elliotf/corexy-printer/main.scad

include <config.scad>;
include <positions.scad>;
include <boxcutter.scad>;
use <util.scad>;
use <belt_retainer.scad>;

module debug_lines() {
  color("red") % translate([20,0,0]) {
    cube([40,.5,.5],center=true);
  }
  color("green") % translate([0,20,0]) {
    cube([.5,40,.5],center=true);
  }
  color("blue") % translate([0,0,20]) {
    cube([.5,.5,40],center=true);
  }
}

module z_line_bearing() {
  difference() {
    hole(z_line_bearing_diam,z_line_bearing_thickness,resolution);
    hole(z_line_bearing_inner,z_line_bearing_thickness+1,resolution);
  }
}

module line_hole() {
  accurate_circle(3,resolution);
}

module zip_tie_hole(diam,width=zip_tie_width,thickness=zip_tie_thickness) {
  difference() {
    hole(diam+thickness*2,width,resolution);
    hole(diam,width+.1,resolution);
  }
}

module bevel_hole(diam,height,sides) {
  hull() {
    hole(diam+height*2,extrusion_height,sides);
    hole(diam,extrusion_height+height*2.2,sides);
  }
}

module line_bearing() {
  res = 64;

  module body() {
    for(side=[top,bottom]) {
      hull() {
        translate([0,0,-side*(line_bearing_thickness/4)]) {
          hole(line_bearing_effective_diam,line_bearing_thickness/2,res);
        }
        translate([0,0,-side*(line_bearing_thickness/2-0.05)]) {
          hole(line_bearing_diam,0.1,res);
        }
      }
    }
  }

  module holes() {
    hole(line_bearing_inner, line_bearing_thickness+1,res);
  }

  difference() {
    body();
    holes();
  }
}

module bevel_lipped_hole(diam=m3_diam,height=spacer,sides=8,lip_width=1) {
  difference() {
    hull() {
      translate([0,0,height/2]) {
        hole(diam+lip_width*2,height,sides);
      }

      translate([0,0,-.5]) {
        hole(diam+lip_width*2+height*2,1,sides);
      }
    }

    hole(diam,height*3,sides);
  }
}

module line_bearing_bevel(sides=[top,bottom], resolution=8, hole_resolution=8, spacing=line_bearing_thickness+line_bearing_washer_thickness*2) {
  difference() {
    for(side=sides) {
      translate([0,0,(spacing/2)*side]) {
        hull() {
          hole(line_bearing_inner+1,line_bearing_washer_thickness*2,resolution);
          translate([0,0,line_bearing_washer_thickness*side]) {
            hole(line_bearing_inner+4,line_bearing_washer_thickness,resolution);
          }
        }
      }
    }

    hole(line_bearing_inner,line_bearing_thickness*3,hole_resolution);
  }
}

module hotend() {
  e3d_hotend();
}

module e3d_hotend() {
  module body() {
    hotend_mount_height    = hotend_height_above_groove + hotend_groove_height + hotend_height_below_groove;

    translate([0,0,-hotend_height_above_groove/2]) {
      hole(hotend_mount_diam,hotend_height_above_groove,resolution);
    }
    translate([0,0,-hotend_height_above_groove-hotend_groove_height/2]) {
      hole(hotend_groove_diam,hotend_groove_height+1,resolution);
    }
    translate([0,0,-hotend_height_above_groove-hotend_groove_height-hotend_height_below_groove/2-10]) {
      hole(hotend_mount_diam,hotend_height_below_groove+20,resolution);
    }

    num_fins      = 11;
    fin_thickness = 1;
    fin_spacing   = 2.5;

    translate([0,0,-hotend_dist_to_heatsink_bottom+fin_thickness/2]) {
      for(z=[0:10]) {
        translate([0,0,fin_spacing*z]) {
          hole(hotend_heatsink_diam,fin_thickness,resolution);
        }
      }
    }

    translate([0,0,-hotend_len]) {
      hull() {
        translate([0,0,0.5]) {
          hole(.5,1,36);
        }
        translate([0,0,3.5]) {
          hole(4,2,36);
        }
      }

      translate([0,-20/2+4.5,5+11.5/2]) {
        cube([16,20,11.5],center=true);
      }
    }
  }

  module holes() {
    //hole(filament_diam,hotend_len*3,8);
  }

  difference() {
    body();
    holes();
  }
}

module jhead_hotend() {
  module body() {
    height_groove_and_above = hotend_clamped_height;
    height_below_groove = hotend_len - height_groove_and_above;

    translate([0,0,-hotend_height_above_groove/2]) {
      hole(hotend_diam,hotend_height_above_groove,90);
    }
    translate([0,0,-hotend_height_above_groove-hotend_groove_height/2]) {
      hole(hotend_groove_diam,hotend_groove_height,90);
    }
    translate([0,0,-height_groove_and_above-height_below_groove/2]) {
      hole(hotend_diam,height_below_groove,90);
    }
  }

  module holes() {
    hole(filament_diam,hotend_len*3,8);
  }

  difference() {
    body();
    holes();
  }
}

module motor() {
  difference() {
    translate([0,0,-motor_side/2]) cube([motor_side,motor_side,motor_side],center=true);
    for(end=[left,right]) {
      for(side=[front,rear]) {
        translate([motor_hole_spacing/2*side,motor_hole_spacing/2*end,0]) cylinder(r=motor_screw_diam/2,h=100,center=true);
      }
    }
  }

  translate([0,0,motor_shaft_len/2]) cylinder(r=motor_shaft_diam/2,h=motor_shaft_len,center=true);
}

module motor_sheet_holes() {
  accurate_circle(z_motor_shoulder_diam,resolution);

  for(x=[left,right]) {
    for(y=[top,bottom]) {
      translate([nema17_hole_spacing/2*x,nema17_hole_spacing/2*y]) {
        accurate_circle(nema17_screw_diam,resolution);
      }

      rotate([0,0,45]) {
        translate([nema14_hole_spacing/2*x,nema14_hole_spacing/2*y]) {
          accurate_circle(nema14_screw_diam,resolution);
        }
      }
    }
  }
}

module hotend_zip_tie_holes() {
  hotend_clearance = 0.1;
  hotend_res = resolution;
  above_height = hotend_height_above_groove+hotend_clearance*2;
  translate([0,-hotend_diam/2,0]) {
    cube([hotend_groove_diam-0.2,hotend_diam,30],center=true);
  }

  for(side=[top,bottom]) {
    translate([0,-hotend_mount_diam/2,side*(hotend_groove_height)]) {
      cube([hotend_mount_diam-0.2,hotend_mount_diam,hotend_groove_height],center=true);
    }
  }

  // zip tie restraint
  zip_tie_hole(hotend_diam + wall_thickness);

  rotate([0,0,-45]) {
    translate([hotend_diam/2-3,-hotend_diam/2,0]) {
      cube([hotend_diam,hotend_diam,hotend_groove_height+hotend_height_above_groove*2+0.05],center=true);
    }
  }
}

module hotend_groove_mount_void() {
  hotend_clearance = 0.1;
  hotend_res = resolution;
  above_height = hotend_height_above_groove+hotend_clearance*2;
  rotate([0,0,90]) {
    translate([0,0,-hotend_height_above_groove-hotend_groove_height/2]) {
      translate([0,-hotend_diam/2,0]) {
        cube([hotend_groove_diam,hotend_diam,30],center=true);
      }
    }

    translate([0,0,-above_height/2+hotend_clearance]) {
      hole(hotend_groove_diam+hotend_clearance,above_height,hotend_res);
      translate([0,-hotend_diam/2,0]) {
        cube([hotend_diam,hotend_diam,above_height],center=true);
      }
    }

    // zip tie restraint
    translate([0,0,-above_height/2]) {
      zip_tie_hole(hotend_diam + wall_thickness*2.5);
    }

    translate([0,0,-hotend_clamped_height-10+hotend_clearance]) {
      hole(hotend_diam+hotend_clearance,20,hotend_res);
      translate([0,-hotend_diam/2,0]) {
        cube([hotend_diam,hotend_diam,20],center=true);
      }
    }
  }
}

module x_carriage() {
  body_side        = rear;
  fan_side         = 30;
  fan_diam         = fan_side-wall_thickness*2;
  fan_screw_diam   = 2.6;
  fan_screw_depth  = 7;
  fan_thickness    = 10;
  fan_pos_y        = front*(x_bearing_diam/2+30/2+wall_thickness/2);
  fan_pos_z        = hotend_z-hotend_dist_to_heatsink_bottom+fan_side/2;
  fan_hole_spacing = 24;
  heatsink_pos_z   = hotend_z-hotend_len+hotend_nozzle_to_bottom_fin+hotend_heatsink_height/2;
  heatsink_pos_z   = hotend_z-hotend_dist_to_heatsink_bottom+hotend_heatsink_height/2;

  bearing_body_wall_thickness = top_line_pos_y-x_bearing_diam/2;
  bearing_body_diam = x_bearing_diam+wall_thickness*3;
  bearing_body_diam = x_bearing_diam + bearing_body_wall_thickness*2;

  body_depth  = top_line_pos_y - bottom_line_pos_y;
  body_height = x_rod_spacing;

  tuner_mount_width  = x_carriage_width;
  tuner_mount_depth  = tuner_shaft_screwed_diam+wall_thickness*3;
  tuner_mount_height = tuner_shaft_screwed_len;

  bottom_top_dist_z     = top_line_pos_z - bottom_line_pos_z;
  bottom_top_dist_y     = top_line_pos_y - bottom_line_pos_y;
  bottom_top_dist_angle = sqrt(pow(bottom_top_dist_z,2)+pow(bottom_top_dist_y,2));
  bottom_top_line_angle = atan2(bottom_top_dist_z,bottom_top_dist_y);

  line_hole_opening     = 1.1;

  tuner_rotate_z = 10;
  module position_tuner() {
    translate([tuner_pos_x,tuner_pos_y,top_line_pos_z]) {
      rotate([0,0,tuner_rotate_z]) {
        rotate([0,90,0]) {
          children();
        }
      }
    }
  }

  module body() {
    // bearing holders
    hull() {
      for(side=[top,bottom]) {
        translate([0,0,x_rod_spacing/2*side]) {
          rotate([0,90,0]) {
            hole(bearing_body_diam,x_carriage_width,resolution);
          }
        }
      }
    }

    // tuner retainer body
    hull() {
      translate([0,tuner_pos_y,tuner_shoulder_pos_z-tuner_mount_height/2]) {
        for(y=[front]) {
          for(z=[top,bottom]) {
            translate([0,y*(tuner_mount_depth/2-rounded_diam/2),z*(tuner_mount_height/2-rounded_diam/2)]) {
              rotate([0,90,0]) {
                hole(rounded_diam,tuner_mount_width,resolution);
              }
            }
          }
        }
        for(y=[rear]) {
          for(z=[top,bottom]) {
            translate([0,y*(tuner_mount_depth/2-rounded_diam/2+wall_thickness*z),z*(tuner_mount_height/2-rounded_diam/2)]) {
              rotate([0,90,0]) {
                hole(rounded_diam,tuner_mount_width,resolution);
              }
            }
          }
        }
      }
      // tuner mounting
      for(side=[left,right]) {
        mirror([1-side,0,0]) {
          position_tuner() {
            translate([tuner_anchor_screw_hole_pos_x,tuner_anchor_screw_hole_pos_y,tuner_anchor_screw_hole_pos_z]) {
              rotate([0,90,0]) {
                translate([0,0,2.5]) {
                  hole(tuner_anchor_screw_hole_diam+wall_thickness*2,3,resolution);
                }
              }
            }
          }
        }
      }
    }

    // hotend mount
    hull() {
      translate([-x_carriage_width/2+1,0,x_rod_spacing/2]) {
        rotate([0,90,0]) {
          hole(bearing_body_diam,2,8);
        }
      }
      translate([0,hotend_y,hotend_z-hotend_height_above_groove/2]) {
        hole(hotend_mount_diam+wall_thickness*3,0.1,resolution);

        translate([-x_carriage_width/2+hotend_groove_diam/2,0,0]) {
          hole(hotend_groove_diam,0.1,8);
        }
      }
      translate([0,hotend_y,fan_pos_z]) {
        hole(hotend_diam+wall_thickness*3,fan_side,resolution);
      }
      translate([-x_carriage_width/2+wall_thickness*2,0,fan_pos_z]) {
        cube([wall_thickness*4,1,fan_side],center=true);
      }
      translate([x_carriage_width/2-1,-bearing_body_diam/4,fan_pos_z]) {
        cube([2,bearing_body_diam/2,fan_side],center=true);
      }
      translate([-x_carriage_width/2+wall_thickness*2,fan_pos_y,fan_pos_z]) {
        for(y=[front]) {
          for(z=[top,bottom]) {
            translate([0,(fan_side/2-rounded_diam/2)*y,(fan_side/2-rounded_diam/2)*z]) {
              rotate([0,90,0]) {
                hole(rounded_diam,wall_thickness*4,resolution);
              }
            }
          }
        }
      }
    }

    rounded_diam = 5;
    // conntect top bearing to tuner mount
    hull() {
      translate([0,tuner_pos_y,tuner_shoulder_pos_z-tuner_mount_height/2]) {
        translate([0,front*(tuner_mount_depth/2-rounded_diam/2),tuner_mount_height/2-rounded_diam/2]) {
          rotate([0,90,0]) {
            hole(rounded_diam,tuner_mount_width,resolution);
          }
        }
      }

      translate([0,0,x_rod_spacing/2]) {
        rotate([0,90,0]) {
          hole(bearing_body_diam,x_carriage_width,resolution);
        }
      }
    }
  }

  module holes() {
    // hotend mount
    hotend_groove_depth = (hotend_diam - hotend_groove_diam)/2;
    translate([0,hotend_y,hotend_z-hotend_height_above_groove-hotend_groove_height/2]) {
      zip_tie_hole(hotend_groove_diam+wall_thickness*3);
    }

    translate([0,hotend_y,hotend_z-hotend_len/2]) {
      hull() {
        for(r=[0,-60]) {
          rotate([0,0,r]) {
            translate([20,1,0]) {
              cube([40,2,hotend_len+10],center=true);
            }
          }
        }
      }
    }
    translate([hotend_groove_diam*.8,hotend_y-hotend_groove_diam,hotend_z-hotend_len/2]) {
      //cube([hotend_groove_diam,hotend_groove_diam*1.5,hotend_len+1],center=true);
    }

    groove_slop = 0.1;
    translate([0,hotend_y,hotend_z-groove_slop/2]) {
      hole(hotend_mount_diam,hotend_height_above_groove*2,resolution);

      translate([20,0,0]) {
        cube([40,hotend_mount_diam-0.1,hotend_height_above_groove*2],center=true);
      }
    }
    translate([0,hotend_y,hotend_z-hotend_height_above_groove-hotend_groove_height/2]) {
      hole(hotend_groove_diam,hotend_groove_height*2,resolution);

      translate([20,0,0]) {
        cube([40,hotend_groove_diam-0.1,hotend_groove_height*2],center=true);
      }
    }
    translate([0,hotend_y,hotend_z-hotend_height_above_groove-hotend_groove_height-10+groove_slop/2]) {
      hole(hotend_mount_diam,20,resolution);

      translate([20,0,0]) {
        cube([40,hotend_mount_diam-0.1,20],center=true);
      }
    }
    hull() {
      translate([-x_carriage_width/2,fan_pos_y,fan_pos_z]) {
        rotate([0,90,0]) {
          hole(fan_diam,fan_thickness*3,resolution);
        }
      }
      translate([0,hotend_y,fan_pos_z]) {
        hole(hotend_diam,1,resolution);
      }
    }
    translate([-x_carriage_width/2,fan_pos_y,fan_pos_z]) {
      for(y=[front,rear]) {
        for(z=[top,bottom]) {
          translate([0,fan_hole_spacing/2*y,fan_hole_spacing/2*z]) {
            rotate([0,90,0]) {
              hole(fan_screw_diam,fan_screw_depth*2,8);
            }
          }
        }
      }
    }
    translate([0,hotend_y,heatsink_pos_z-0.05]) {
      hole(hotend_diam,hotend_heatsink_height+0.1,resolution);

      translate([20,0,0]) {
        cube([40,hotend_diam-0.1,hotend_heatsink_height+0.1],center=true);
      }
    }

    tuner_hollow_nut_height = tuner_mount_height*.75;
    // tuner mounting
    for(side=[left,right]) {
      mirror([1-side,0,0]) {
        position_tuner() {
          translate([tuner_anchor_screw_hole_pos_x,tuner_anchor_screw_hole_pos_y,tuner_anchor_screw_hole_pos_z]) rotate([0,90,0]) {
            rotate([0,0,tuner_rotate_z]) {
              hole(tuner_anchor_screw_hole_diam,12,8);
            }
          }
        }
      }
      translate([tuner_pos_x*side,tuner_pos_y,0]) {
        // main hole and screw hole
        translate([0,0,tuner_shoulder_pos_z]) {
          hole(tuner_shaft_screw_diam,tuner_mount_height*2+1,8);
          hole(tuner_shaft_screwed_diam,21,8);

          translate([0,0,-tuner_mount_height-tuner_hollow_nut_height/2]) {
            hole(tuner_nut_max_diam,tuner_hollow_nut_height,resolution);
          }
        }
      }
    }

    // reinforcements
    for(z=[1,3,5]) {
      translate([0,tuner_pos_y+tuner_mount_depth/2+1,tuner_shoulder_pos_z-3*z]) {
        cube([1,tuner_mount_depth+tuner_shaft_screwed_diam,1],center=true);
      }
    }

    // line path
    translate([0,top_line_pos_y,top_line_pos_z]) {
      rotate([bottom_top_line_angle,0,0]) {
        rotate([0,90,0]) {
          hole(line_hole_opening,x_carriage_width+1,8);
        }
      }
    }
    hull() {
      translate([0,-x_bearing_diam/8,0]) {
        rotate([0,90,0]) {
          hole(line_hole_opening*2,x_carriage_width+1,8);
        }
      }
      translate([0,bottom_line_pos_y,bottom_line_pos_z]) {
        rotate([bottom_top_line_angle,0,0]) {
          rotate([0,90,0]) {
            hole(line_hole_opening,x_carriage_width+1,8);
          }
        }
      }
    }
    front_to_back_line_path_diam = bottom_top_dist_angle-line_hole_opening;
    for(side=[left,right]) {
      translate([(x_carriage_width/2-front_to_back_line_path_diam/2-.5)*side,top_line_pos_y-bottom_top_dist_y/2,top_line_pos_z-bottom_top_dist_z/2]) {
        rotate([bottom_top_line_angle,0,0]) {
          difference() {
            translate([side*(bottom_top_dist_angle/2-2),2,0]) {
              cube([bottom_top_dist_angle/2+2,bottom_top_dist_angle+4,line_hole_opening],center=true);
            }
            hole(front_to_back_line_path_diam,line_hole_opening+1,resolution);
          }
        }
      }
    }
    translate([extrusion_height,-1,x_rod_spacing/2+x_bearing_diam/2]) {
      rotate([0,0,0]) {
        cube([x_carriage_width,5,x_bearing_diam],center=true);
      }
    }
    translate([extrusion_height,0,-x_rod_spacing/2-x_bearing_diam]) {
      rotate([45,0,0]) {
        cube([x_carriage_width,x_bearing_diam*1.5,x_bearing_diam*1.5],center=true);
      }
    }

    for(side=[top,bottom]) {
      translate([0,0,x_rod_spacing/2*side]) {
        rotate([0,90,0]) {
          // bearing hole
          hole(x_bearing_diam,x_carriage_width+1,16);
          // beveled opening
          for(end=[left,right]) {
            hull() {
              translate([0,0,(x_carriage_width/2)*end]) {
                hole(x_bearing_diam,3,16);
                translate([0,0,.5*end]) {
                  hole(x_bearing_diam+1,1,16);
                }
              }
            }
          }
        }
      }
    }

    translate([extrusion_height,-x_bearing_diam/4,0]) {
      //cube([x_carriage_width,x_bearing_diam/2,x_rod_spacing],center=true);
    }

    translate([0,hotend_y,hotend_z]) {
      % hotend();
    }

    translate([-x_carriage_width/2-5,fan_pos_y,fan_pos_z]) {
      % cube([fan_thickness,fan_side,fan_side],center=true);
    }
  }
  translate([0,top_line_pos_y,top_line_pos_z]) {
    //color("green") % cube([x_carriage_width+60,0.8,0.8],center=true);
  }
  translate([0,bottom_line_pos_y,bottom_line_pos_z]) {
    //color("red") % cube([x_carriage_width+60,0.8,0.8],center=true);
  }

  for(side=[left,right]) {
    mirror([1+side,0,0]) {
      position_tuner() {
        % tuner();
      }
    }
  }

  difference() {
    body();
    holes();
  }

  % for(side=[top,bottom]) {
    translate([0,0,x_rod_spacing/2*side]) {
      rotate([0,90,0]) {
        cylinder(r=x_bearing_diam/2,h=x_bearing_len,center=true);
      }
    }
  }

  translate([0,hotend_y,hotend_z]) {
    //% hotend();
  }
}

module y_carriage() {
  line_bearing_x              = (y_rod_x - y_carriage_line_bearing_x);
  line_bearing_opening_height = line_bearing_thickness*2+line_bearing_washer_thickness*3;
  rod_hole_diam               = x_rod_diam + rod_slop;
  x_rod_clamp_len             = y_carriage_width;

  rounded_diam = y_rod_diam+rod_slop+min_material_thickness*4;
  total_height = x_rod_spacing + rounded_diam;

  module body() {
    // main body, hold x rods
    hull() {
      for(side=[top,bottom]) {
        translate([x_rod_clamp_len/2,-x_rod_diam,x_rod_spacing/2*side]) {
          rotate([0,90,0]) {
            hole(rounded_diam,x_rod_clamp_len,resolution);
          }
        }

        translate([x_rod_clamp_len/2,front*(y_bearing_len/2-line_bearing_diam*.75),0]) {
          rotate([0,90,0]) {
            hole(line_bearing_diam,x_rod_clamp_len,resolution);
          }
        }

        translate([x_rod_clamp_len/2,rear*(y_bearing_len/2-rounded_diam/4),(total_height/2-rounded_diam/4)*side]) {
          rotate([0,90,0]) {
            hole(rounded_diam/2,x_rod_clamp_len,resolution);
          }
        }

        intersection() {
          translate([y_bearing_diam/2,0,0]) {
            cube([y_bearing_diam,y_bearing_len*2,y_bearing_diam*2],center=true);
          }
          rotate([90,0,0]) {
            hole(y_bearing_diam+6,y_bearing_len,resolution);
          }
        }
      }
      translate([line_bearing_x,y_carriage_line_bearing_y,y_carriage_line_bearing_z]) {
        cube([line_bearing_diam,line_bearing_diam+spacer*2+extrusion_width*6,line_bearing_opening_height+2],center=true);
      }
    }
  }

  module holes() {
    // x rods and clamps
    for(side=[top,bottom]) {
      translate([x_rod_clamp_len/2,0,x_rod_spacing/2*side]) {
        rotate([0,90,0]) {
          hole(rod_hole_diam+rod_slop,x_rod_clamp_len+4,16);

          for(end=[left,right]) {
            translate([0,0,(x_rod_clamp_len/2+.5)*end]) {
              hull() {
                hole(rod_hole_diam,3,16);
                hole(rod_hole_diam+1,1,16);
              }
            }
          }
        }

        translate([-extrusion_height,20,0]) {
          cube([x_rod_clamp_len,40,2],center=true);
        }
        hull() {
          translate([-extrusion_height,0,0]) {
            rotate([0,90,0]) {
              hole(2,x_rod_clamp_len,16);
            }
            translate([0,-x_rod_diam,0]) {
              rotate([0,90,0]) {
                hole(2,x_rod_clamp_len,16);
              }
            }
          }
        }
      }
    }

    // zip tie to secure the carriage to the y rod bearing
    translate([0,-rod_hole_diam/2-zip_tie_width,0]) {
      rotate([90,0,0]) {
        zip_tie_hole(y_bearing_diam+min_material_thickness*2);
      }
    }

    // y rod bearing and clamp
    translate([0,0,0]) {
      rotate([90,0,0]) {
        hole(y_bearing_diam,y_bearing_len*2,16);
      }
    }

    // bearing/line-related holes
    translate([line_bearing_x-line_bearing_effective_diam/2-0.4,y_carriage_line_bearing_y,0]) {
      translate([0,-y_bearing_len,to_front_line_z]) {
        rotate([90,0,0]) {
          hole(2,y_bearing_len*2,8);
        }
      }
      translate([0,y_bearing_len,to_rear_line_z]) {
        rotate([90,0,0]) {
          hole(2,y_bearing_len*2,8);
        }
      }
    }
    translate([line_bearing_x,y_carriage_line_bearing_y,y_carriage_line_bearing_z]) {
      // bearing/clamp screw
      hole(line_bearing_inner+rod_slop,50,8);

      // captive nut
      translate([0,0,-total_height/2]) {
        hole(line_bearing_nut_diam,4,6);
      }

      hull() {
        hole(line_bearing_diam + spacer*2,line_bearing_opening_height,resolution);
        // room for belt/filament
        translate([line_bearing_diam/2,0,0]) {
          cube([line_bearing_diam+spacer*2,line_bearing_diam+spacer*2,line_bearing_opening_height],center=true);
        }
      }

      for (side=[top,bottom]) {
        translate([0,0,(line_bearing_thickness/2+line_bearing_washer_thickness/2)*side]) {
          % line_bearing();
        }
      }
    }
  }

  module bridges() {
    for(side=[top,bottom]) {
      translate([line_bearing_x,y_carriage_line_bearing_y,y_carriage_line_bearing_z+side*(line_bearing_washer_thickness/2+line_bearing_thickness/2)]) {
        line_bearing_bevel([side]);
      }
    }
  }

  difference() {
    body();
    holes();
  }
  bridges();

  translate([0,0,0]) {
    rotate([90,0,0]) {
      % cylinder(r=y_bearing_diam/2,h=y_bearing_len,center=true);
    }
  }
}

module handle() {
  module body() {
    hull() {
      translate([0,-handle_attachment_height/2,0]) {
        cube([handle_hole_width+handle_material_width*2,handle_attachment_height,sheet_thickness],center=true);
      }

      for(x=[left,right]) {
        translate([x*(handle_hole_width/2+handle_material_width/2-5),handle_hole_height+handle_material_width/2,0]) {
          hole(handle_material_width,sheet_thickness,resolution);
        }
      }
    }
  }

  module holes() {
    hull() {
      for(x=[left,right]) {
        translate([x*(handle_hole_width/2-handle_material_width/2),handle_hole_height/2+top*(handle_hole_height/2-handle_material_width/2),0]) {
          hole(handle_material_width,sheet_thickness+1,resolution);
        }
        translate([x*(handle_hole_width/2-handle_material_width/2),handle_hole_height/2+bottom*(handle_hole_height/2-handle_material_width/2),0]) {
          hole(handle_material_width,sheet_thickness+1,resolution);
        }
      }
    }
  }

  difference() {
    body();
    holes();
  }
}

module front_sheet() {
  rounded_diam = bc_shoulder_width*2;

  module body() {
    width  = front_sheet_width + sheet_thickness*2 + bc_shoulder_width*2;
    height = sheet_height      + sheet_thickness + bc_shoulder_width;
    intersection() {
      box_side([front_sheet_width,sheet_height],[0,4,4,4]);
      translate([0,-sheet_thickness/2-bc_shoulder_width/2]) {
        hull() {
          for(x=[left,right]) {
            for(y=[top,bottom]) {
              translate([x*(width/2-rounded_diam/2),y*(height/2-rounded_diam/2),0]) {
                accurate_circle(rounded_diam,resolution);
              }
            }
          }
        }
      }
    }
  }

  module holes() {
    translate([0,-sheet_pos_z,0]) {
      translate([0,top_sheet_pos_z,0]) {
        box_holes_for_side(front_sheet_width,4);
      }

      for(side=[left,right]) {
        translate([y_rod_x*side,0,0]) {
          accurate_circle(y_rod_diam-laser_cut_kerf*2,64);
        }

        translate([return_line_x*side,return_line_z,0]) {
          line_hole();
        }

        translate([xy_line_x*side,to_front_line_z,0]) {
          line_hole();
        }

        translate([xy_motor_pos_x*side,xy_motor_pos_z,0]) {
          rotate([0,0,0]) {
            motor_sheet_holes();
          }
        }
      }
    }

    // rounded top opening
    for(side=[left,right]) {
      translate([side*(front_opening_width/2-sheet_thickness),sheet_height/2,0]) {
        difference() {
          square([rounded_diam,rounded_diam],center=true);
          translate([rounded_diam/2*side,-rounded_diam/2,0]) {
            accurate_circle(rounded_diam,resolution);
          }
        }
      }
    }

    front_opening_width = main_opening_width - sheet_thickness*2;
    hull() {
      translate([0,sheet_height/2,0]) {
        for(side=[left,right]) {
          translate([side*(build_x/2-sheet_thickness-rounded_diam/2),-main_opening_height+rounded_diam/2,0]) {
            accurate_circle(rounded_diam,resolution);
          }
          translate([side*(front_opening_width/2-sheet_thickness-rounded_diam/2),-hotend_sheet_clearance+rounded_diam/2,0]) {
            accurate_circle(rounded_diam,resolution);
          }
        }
        square([front_opening_width-sheet_thickness*2,2],center=true);
      }
    }
  }

  difference() {
    body();
    holes();
  }
}

module rear_sheet() {
  rounded_diam = bc_shoulder_width*2;

  module body() {
    width  = front_sheet_width + sheet_thickness*2 + bc_shoulder_width*2;
    height = sheet_height      + sheet_thickness + bc_shoulder_width;
    intersection() {
      box_side([front_sheet_width,sheet_height],[0,4,4,4]);
      translate([0,-sheet_thickness/2-bc_shoulder_width/2]) {
        hull() {
          for(x=[left,right]) {
            for(y=[top,bottom]) {
              translate([x*(width/2-rounded_diam/2),y*(height/2-rounded_diam/2),0]) {
                accurate_circle(rounded_diam,resolution);
              }
            }
          }
        }
      }
    }
  }

  module holes() {
    translate([0,-sheet_pos_z]) {
      translate([0,top_sheet_pos_z]) {
        box_holes_for_side(front_sheet_width,4);
      }
      for(side=[left,right]) {
        translate([y_rod_x*side,0,0]) {
          accurate_circle(y_rod_diam-laser_cut_kerf*2,64);
        }

        translate([xy_line_x*side,0]) {
          translate([0,to_rear_line_z]) {
            line_hole();
          }
        }
        translate([return_line_x*side,0]) {
          translate([0,return_line_z]) {
            line_hole();
          }
        }
      }

      translate([z_brace_sheet_pos_x,z_brace_sheet_pos_z,0]) {
        rotate([0,0,90]) {
          box_holes_for_side(z_brace_height,4);
        }
      }
    }

    rounded_diam       = 10;
    main_hole_width    = z_rod_pos_x*1.8;
    material_remaining = 0;
    main_hole_height   = motor_side*2;

    translate([0,-sheet_pos_z]) {
      translate([z_motor_pos_x,z_motor_pos_z]) {
        motor_sheet_holes();
      }
    }
    translate([z_idler_pulley_pos_x,z_idler_pulley_pos_z-sheet_pos_z]) {
      accurate_circle(bearing_625_diam-2,32);
      position_z_pulley_bearing_retaimer_mount_holes() {
        accurate_circle(3,8);
      }
    }

    brace_side_hole_x = z_brace_sheet_pos_x + z_motor_side * (sheet_thickness/2 + bc_shoulder_width + rounded_diam/2);
    other_side_hole_x = z_motor_side*(main_hole_width/2-rounded_diam/2);
    if (main_hole_height) {
      hull() {
        //translate([z_motor_pos_x + motor_side/2 + main_hole_width/2,-side_sheet_height/2+height_below_top_sheet/2]) {
        translate([0,-side_sheet_height/2+height_below_top_sheet/2]) {
          for(x=[brace_side_hole_x,other_side_hole_x]) {
            for(y=[front,rear]) {
              translate([x,(main_hole_height/2-rounded_diam)*y]) {
                accurate_circle(rounded_diam,resolution);
              }
            }
          }
        }
      }
    }
  }

  difference() {
    body();
    holes();
  }
}

module side_sheet() {
  bottom_material  = 30;
  hotend_clearance = -1*(hotend_z-hotend_len/2-top_of_sheet);

  opening_height = min((sheet_height - bottom_material),(sheet_height*.5));

  module body() {
    box_side([side_sheet_depth,side_sheet_height],[0,3,4,3]);
  }

  height_below_top_sheet = abs(-sheet_pos_z+top_sheet_pos_z + side_sheet_height/2);

  module holes() {
    translate([0,-sheet_pos_z+top_sheet_pos_z]) {
      box_holes_for_side(side_sheet_depth,4);
    }

    rounded_diam     = 10;
    main_hole_depth  = side_sheet_depth       - motor_side*2.5;
    main_hole_height = height_below_top_sheet - motor_side*2.5;

    hull() {
      translate([0,-side_sheet_height/2+height_below_top_sheet/2]) {
        for(x=[left,right]) {
          for(y=[front,rear]) {
            translate([(main_hole_depth/2-rounded_diam)*x,(main_hole_height/2-rounded_diam)*y]) {
              accurate_circle(rounded_diam,resolution);
            }
          }
        }
      }
    }
  }

  difference() {
    body();
    holes();
  }
}

module top_sheet() {
  module body() {
    box_side([top_sheet_width,top_sheet_depth],[3,3,3,3]);
  }

  module holes() {
    hole_diam = 6*2;
    front_y   = front*top_sheet_depth/2;

    front_opening_width = main_opening_width - sheet_thickness*2;

    hull() {
      for(x=[left,right]) {
        for(y=[front_y+hole_diam,front_y+main_opening_depth-hole_diam/2]) {
          translate([x*(main_opening_width/2-hole_diam/2),y]) {
            accurate_circle(hole_diam,resolution);
          }
        }
      }
      translate([0,front*(top_sheet_depth/2-sheet_thickness/2+0.05)]) {
        square([front_opening_width-hole_diam,sheet_thickness],center=true);
      }
    }
    translate([0,front*(top_sheet_depth/2)]) {
      square([front_opening_width-sheet_thickness*2,sheet_thickness*4],center=true);
    }

    for(side=[left,right]) {
      translate([z_rod_pos_x*side,z_rod_pos_y]) {
        accurate_circle(z_rod_diam-laser_cut_kerf*2,64);
      }
    }
  }

  difference() {
    body();
    holes();
  }
}

module bottom_sheet() {
  width = side_sheet_pos_x*2 - sheet_thickness;
  depth = sheet_pos_y*2 - sheet_thickness;

  module body() {
    box_side([width,top_sheet_depth],[3,3,3,3]);
  }

  module holes() {
    for(side=[left,right]) {
      translate([z_rod_pos_x*side,z_rod_pos_y,0]) {
        accurate_circle(z_rod_diam-laser_cut_kerf*2,64);
      }
    }

    translate([z_line_bearing_diam/2+belt_thickness/2+tensioner_belt_dist_x,z_rod_pos_y+tensioner_belt_dist_y]) {
      accurate_circle(3,64);
    }
  }

  difference() {
    body();
    holes();
  }
}

module line_bearing_body_base() {
  for(x=[left,right]) {
    for(y=[front,rear]) {
      translate([(bearing_body_depth/2-wall_thickness)*x,0,(bearing_body_thickness/2-wall_thickness)*y]) {
        rotate([90,0,0]) {
          hole(wall_thickness*2,line_bearing_mount_thickness,resolution);
        }
      }
    }
  }
}

module line_bearing_body(side=top,height=(line_bearing_mount_thickness+line_bearing_nut_diam/2+spacer)) {
  hull() {
    translate([0,side*(height-line_bearing_mount_thickness/2),0]) {
      line_bearing_body_base();
    }
    hole(bearing_body_diam,bearing_body_thickness,resolution);
  }
}

module line_bearing_holes(side=top,height=(line_bearing_mount_thickness+line_bearing_nut_diam/2+spacer)) {
  hole(line_bearing_diam+spacer*2,line_bearing_thickness+line_bearing_washer_thickness*2,resolution);
  hole(line_bearing_inner,bearing_body_thickness+0.5,8);

  translate([0,0,-bearing_body_thickness/2*side]) {
    rotate([0,0,90]) {
      hole(line_bearing_nut_diam,line_bearing_nut_thickness,6);
    }
  }
}

module front_xy_endcap() {
  wall_thickness  = extrusion_width*4;

  bearing_y = front*(line_bearing_mount_thickness+line_bearing_nut_diam/2+spacer);
  bearing_z = to_front_line_z-line_bearing_effective_diam/2;

  dist_to_motor_z = to_rear_line_z - xy_motor_pos_z;
  dist_to_motor_x = abs(xy_line_x - (xy_motor_pos_x-pulley_diam/2));
  dist_to_motor_x = abs(xy_line_x - (xy_motor_pos_x));

  to_carriage_bearing_angle = atan((dist_to_motor_x+pulley_diam/2)/dist_to_motor_z);
  to_rear_bearing_angle = atan((dist_to_motor_x-pulley_diam/2)/dist_to_motor_z);

  module pos_zero() {
    translate([-y_rod_x,0,0]) {
      children();
    }
  }

  module to_carriage_bearing_pos() {
    dist_to_motor_x           = abs(xy_line_x - (xy_motor_pos_x+pulley_diam/2));
    dist_to_motor_z           = to_front_line_z - xy_motor_pos_z;
    to_carriage_bearing_angle = atan(dist_to_motor_x/dist_to_motor_z);

    pos_zero() {
      translate([xy_line_x,bearing_y,to_front_line_z]) {
        rotate([0,to_carriage_bearing_angle,0]) {
          translate([0,0,-line_bearing_effective_diam/2]) {
            rotate([0,90,0]) {
              children();
            }
          }
        }
      }
    }
  }

  module to_rear_bearing_pos() {
    pos_x                 = -y_rod_x+return_line_x;
    dist_to_motor_x       = return_line_x - (xy_motor_pos_x-pulley_diam/2);
    dist_to_motor_z       = return_line_z - xy_motor_pos_z;
    to_rear_bearing_angle = atan(dist_to_motor_x/dist_to_motor_z);

    translate([pos_x,bearing_y,return_line_z]) {
      rotate([0,to_rear_bearing_angle,0]) {
        translate([0,0,-line_bearing_effective_diam/2]) {
          rotate([0,90,0]) {
            children();
          }
        }
      }
    }
  }

  module body() {
    hull() {
      // rod body
      translate([0,-line_bearing_mount_thickness/2,0]) {
        rotate([90,0,0]) {
          hole(y_rod_diam+wall_thickness*3,line_bearing_mount_thickness,resolution);
        }
      }
      translate([0,-line_bearing_mount_thickness/2,0]) {
        // side sheet screw hole
        translate([endcap_side_screw_hole_pos_x,0,endcap_side_screw_hole_pos_z]) {
          rotate([90,0,0]) {
            hole(bc_screw_diam+wall_thickness*3,line_bearing_mount_thickness,resolution);
          }
        }
        // top sheet screw hole
        translate([endcap_top_screw_hole_pos_x,0,endcap_top_screw_hole_pos_z]) {
          rotate([90,0,0]) {
            hole(bc_screw_diam+wall_thickness*3,line_bearing_mount_thickness,resolution);
          }
        }
      }
      to_carriage_bearing_pos() {
        translate([0,-bearing_y-line_bearing_mount_thickness/2,0]) {
          line_bearing_body_base();
        }
      }
      to_rear_bearing_pos() {
        translate([0,-bearing_y-line_bearing_mount_thickness/2,0]) {
          line_bearing_body_base();
        }
      }
    }

    to_carriage_bearing_pos() {
      line_bearing_body(rear);
      % line_bearing();
      translate([sheet_height/2,-line_bearing_effective_diam/2,0]) {
        % cube([sheet_height,1,1],center=true);
      }
    }
    to_rear_bearing_pos() {
      line_bearing_body(rear);
      % line_bearing();
      translate([sheet_height/2,0,0]) {
        % cube([sheet_height,1,1],center=true);
      }
    }
  }

  module holes() {
    // side sheet screw hole
    translate([endcap_side_screw_hole_pos_x,0,endcap_side_screw_hole_pos_z]) {
      rotate([90,0,0]) {
        hole(3,50,16);
        bevel_hole(3,.5,16);
      }
    }
    // top sheet screw hole
    translate([endcap_top_screw_hole_pos_x,0,endcap_top_screw_hole_pos_z]) {
      rotate([90,0,0]) {
        hole(3,50,16);
        bevel_hole(3,.5,16);
      }
    }

    pos_zero() {
      translate([xy_line_x,0,to_front_line_z]) {
        rotate([90,0,0]) {
          hole(3,60,resolution);
          bevel_hole(3,.5,resolution);
        }
      }
      translate([return_line_x,0,return_line_z]) {
        rotate([90,0,0]) {
          hole(3,60,resolution);
          bevel_hole(3,.5,resolution);
        }
      }
    }

    to_carriage_bearing_pos() {
      line_bearing_holes(top);
    }

    to_rear_bearing_pos() {
      line_bearing_holes(top);
    }

    // y rod
    rotate([90,0,0]) {
      % hole(y_rod_diam,line_bearing_mount_thickness*2+1,16);
    }
  }

  module bridges() {
    to_carriage_bearing_pos() {
      line_bearing_bevel();
    }
    to_rear_bearing_pos() {
      line_bearing_bevel();
    }
  }

  difference() {
    body();
    holes();
  }
  bridges();
}

module rear_xy_endcap(side) {
  line_x          = xy_line_x-y_rod_x;
  line_to_motor_x = line_x + 2;
  line_to_motor_z = opposite_to_motor_line_z;

  high_bearing_y = line_bearing_mount_thickness + line_bearing_nut_diam/2 + spacer;
  mid_bearing_y  = high_bearing_y;
  line_to_motor_x = endcap_top_screw_hole_pos_x+line_bearing_effective_diam/2;
  line_to_motor_z = endcap_top_screw_hole_pos_z+line_bearing_effective_diam/2;

  low_high_dist_x          = xy_line_x+return_line_x;
  low_high_dist_z          = to_rear_line_z - return_line_z;
  high_to_low_line_angle_y = -atan2(low_high_dist_z,low_high_dist_x);

  module pos_zero() {
    translate([-y_rod_x,0,0]) {
      children();
    }
  }

  module high_bearing_pos() {
    translate([line_x,high_bearing_y,to_rear_line_z]) {
      rotate([0,high_to_low_line_angle_y,0]) {
        translate([-line_bearing_effective_diam/2,0,0]) {
          children();
        }
      }
    }
  }

  module position_clamp() {
    translate([0,line_bearing_mount_thickness,0]) {
      rotate([0,-20,0]) {
        rotate([-90,0,0]) {
          children();
        }
      }
    }
  }

  module mid_bearing_pos() {
    translate([-y_rod_x+return_line_x,mid_bearing_y,return_line_z]) {
      rotate([0,-high_to_low_line_angle_y,0]) {
        translate([-line_bearing_effective_diam/2,0,0]) {
          children();
        }
      }
    }
  }

  module body() {
    hull() {
      // rod body
      translate([0,line_bearing_mount_thickness/2,0]) {
        rotate([90,0,0]) {
          hole(y_rod_diam+wall_thickness*3,line_bearing_mount_thickness,resolution);
        }
      }
      translate([0,line_bearing_mount_thickness/2,0]) {
        // side sheet screw hole
        translate([endcap_side_screw_hole_pos_x,0,endcap_side_screw_hole_pos_z]) {
          rotate([90,0,0]) {
            hole(bc_screw_diam+wall_thickness*3,line_bearing_mount_thickness,resolution);
          }
        }
        // top sheet screw hole
        translate([endcap_top_screw_hole_pos_x,0,endcap_top_screw_hole_pos_z]) {
          rotate([90,0,0]) {
            hole(bc_screw_diam+wall_thickness*3,line_bearing_mount_thickness,resolution);
          }
        }
      }
      high_bearing_pos() {
        translate([0,-high_bearing_y+line_bearing_mount_thickness/2,0]) {
          line_bearing_body_base();
        }
      }
      mid_bearing_pos() {
        translate([0,-mid_bearing_y+line_bearing_mount_thickness/2,0]) {
          line_bearing_body_base();
        }
      }
    }
    high_bearing_pos() {
      line_bearing_body(front);
      % line_bearing();
      translate([-sheet_height/2,line_bearing_effective_diam/2,0]) {
        % cube([sheet_height,1,1],center=true);
      }
    }
    mid_bearing_pos() {
      line_bearing_body(front);
      % line_bearing();
    }
    // rod clamp
    hull() {
      position_clamp() {
        hole(y_rod_diam+wall_thickness*3,line_bearing_mount_thickness*2,resolution);
        translate([y_rod_diam/2+m3_nut_diam/2,0,0]) {
          cube([m3_nut_diam+wall_thickness*2,y_rod_diam+wall_thickness*3,line_bearing_mount_thickness*2],center=true);
        }
      }
    }
  }

  module holes() {
    // side sheet screw hole
    translate([endcap_side_screw_hole_pos_x,0,endcap_side_screw_hole_pos_z]) {
      rotate([90,0,0]) {
        hole(3,50,16);
        bevel_hole(3,.5,16);
      }
    }
    // top sheet screw hole
    translate([endcap_top_screw_hole_pos_x,0,endcap_top_screw_hole_pos_z]) {
      rotate([90,0,0]) {
        hole(3,50,16);
        bevel_hole(3,.5,16);
      }
    }
    high_bearing_pos() {
      line_bearing_holes(-1);
    }
    mid_bearing_pos() {
      line_bearing_holes(-1);
    }

    // line holes
    pos_zero() {
      translate([xy_line_x,0,to_rear_line_z]) {
        rotate([90,0,0]) {
          hole(3,60,resolution);
          bevel_hole(3,.5,resolution);
        }
      }
      translate([return_line_x,0,return_line_z]) {
        rotate([90,0,0]) {
          hole(3,60,resolution);
          bevel_hole(3,.5,resolution);
        }
      }
    }

    // y rod
    position_clamp() {
      hole(y_rod_diam+0.1,line_bearing_mount_thickness*4+1,16);
      translate([0,0,-line_bearing_mount_thickness]) {
        bevel_hole(y_rod_diam+0.1,.5,16);
      }
      translate([y_rod_diam/2+m3_nut_diam/2,0,0]) {
        translate([0,0,extrusion_height]) {
          cube([y_rod_diam*2,2,line_bearing_mount_thickness*2],center=true);

          rotate([90,0,0]) {
            hole(m3_diam,y_rod_diam*2,8);
            translate([0,0,-y_rod_diam/2-wall_thickness*1.5-m3_nut_thickness/2]) {
              rotate([0,0,90]) {
                hole(m3_nut_diam,m3_nut_thickness*2,6);
              }
            }
          }
        }
      }
    }
  }

  module bridges() {
    difference() {
      high_bearing_pos() {
        line_bearing_bevel();
      }
    }
    mid_bearing_pos() {
      line_bearing_bevel();
    }
  }

  difference() {
    body();
    holes();
  }
  bridges();
}

module z_axis_stationary() {
  z_line_bearing_diam = 10;
  motor_pos_z         = top_sheet_pos_z-sheet_thickness/2-motor_side/2;
  motor_pos_z         = bottom_sheet_pos_z+sheet_thickness/2+motor_side/2;

  // z rods
  for (side=[left,right]) {
    translate([z_rod_pos_x*side,z_rod_pos_y,z_rod_pos_z]) {
      % cylinder(r=z_rod_diam/2,h=z_rod_len+0.1,center=true);

      for(end=[top,bottom]) {
        translate([0,0,end*(z_rod_len/2-sheet_thickness-rod_clamp_height/2-0.05)]) {
          rod_clamp(z_rod_diam);
        }
      }
    }
  }

  % translate([z_motor_pos_x,0,z_motor_pos_z]) {
    translate([0,z_line_idler_bearing_pos_y,0]) {
      rotate([90,0,0]) {
        hole(z_pulley_diam,z_pulley_height,resolution);
      }
    }
    translate([0,z_motor_pos_y,0]) {
      rotate([90,0,0]) {
        motor();
      }
    }
  }

  translate([z_idler_pulley_pos_x,0,z_idler_pulley_pos_z]) {
    translate([0,sheet_pos_y,0]) {
      for(side=[front,rear]) {
        translate([0,(bearing_625_thickness/2+sheet_thickness/2)*side,0]) {
          rotate([90*side,0,0]) {
            % bearing_625();

            translate([0,0,-.5]) {
              mirror([0,1-side,0]) {
                z_idler_pulley_bearing_retainer();
              }
            }
          }
        }
      }
    }
    translate([0,z_idler_pulley_pos_y,0]) {
      % rotate([90,0,0]) {
        difference() {
          hole(z_idler_pulley_diam,z_pulley_height,resolution);
          hole(bearing_625_inner,z_pulley_height+1,resolution);
        }
      }
    }
  }
}

module z_carriage_bearing_support_arm() {
  overall_height = z_bed_support_mount_depth+z_bearing_body_diam/2-z_line_bearing_thickness/2;

  echo("overall height: ", overall_height);
  echo("screw length: ", overall_height + z_line_bearing_thickness + sheet_thickness);

  module body() {
    hull() {
      for (side=[top,bottom]) {
        translate([0,0.5,z_carriage_bearing_spacing/2*side]) {
          rotate([90,0,0]) {
            hole(z_line_bearing_diam+wall_thickness*2,1,resolution);
          }
        }

        translate([0,overall_height-2,z_carriage_bearing_spacing/2*side]) {
          rotate([-90,0,0]) {
            hole(z_line_bearing_inner+wall_thickness*2,1,resolution);
          }
        }
        translate([0,overall_height+z_line_bearing_thickness/2,z_carriage_bearing_spacing/2*side]) {
          rotate([-90,0,0]) {
            % z_line_bearing();
          }
        }
      }
    }

    for (side=[top,bottom]) {
      translate([0,overall_height-0.5,z_carriage_bearing_spacing/2*side]) {
        rotate([-90,0,0]) {
          hull() {
            translate([0,0,-1.5]) {
              hole(z_line_bearing_inner+wall_thickness*2,1,resolution);
            }
            hole(z_line_bearing_inner+1,1,resolution);
          }
        }
      }
    }
  }

  module holes() {
    for(side=[top,bottom]) {
      translate([0,0,z_carriage_bearing_spacing/2*side]) {
        rotate([90,0,0]) {
          hole(3,50,16);
        }
      }
    }

    hull() {
      for(side=[top,bottom]) {
        translate([0,0,z_carriage_bearing_spacing*.1*side]) {
          scale([1,1,.75]) {
            rotate([90,0,0]) {
              hole(3,50,16);
            }
          }
        }
      }
    }
  }

  module bridges() {
  }

  difference() {
    body();
    holes();
  }
  bridges();
}

module old_z_carriage_bearing_support_arm() {
  bearing_to_arm_support_dist_y = front*(-z_carriage_bearing_offset_y -z_bearing_body_diam/2 - z_bed_support_mount_depth);

  module body() {
    intersection() {
      hull() {
        for(side=[top,bottom]) {
          translate([z_carriage_bearing_spacing/2*side,0]) {
            accurate_circle(z_line_bearing_diam,resolution);
          }
        }

        translate([0,-bearing_to_arm_support_dist_y-9,0]) {
          square([abs(z_carriage_bearing_offset_z)*2,20],center=true);
        }
      }
      translate([0,-bearing_to_arm_support_dist_y+11,0]) {
        box_side([z_printed_portion_height,22],[0,0,3,0]);
      }
    }
  }

  module holes() {
    for(side=[top,bottom]) {
      translate([z_carriage_bearing_spacing/2*side,0]) {
          accurate_circle(z_line_bearing_inner,resolution);
      }
    }
  }

  difference() {
    body();
    holes();
  }
}

module printed_z_portion() {
  module body() {
    hull() {
      translate([z_rod_pos_x,0,0]) {
        hole(z_bearing_body_diam,z_printed_portion_height,resolution);
      }
      translate([(z_bed_support_pos_x-sheet_thickness/2-z_bed_support_mount_width/2),-z_bearing_body_diam/2+1,0]) {
        cube([z_bed_support_mount_width,2,z_printed_portion_height],center=true);
      }
    }

    translate([(z_bed_support_pos_x-sheet_thickness/2-z_bed_support_mount_width/2),-z_bearing_body_diam/2-z_bed_support_mount_depth/2,0]) {
      cube([z_bed_support_mount_width,z_bed_support_mount_depth,z_printed_portion_height],center=true);

      translate([-(z_bed_support_mount_width/2+z_bed_support_mount_depth/2),0,0]) {
        cube([z_bed_support_mount_depth,z_bed_support_mount_depth,z_printed_portion_height],center=true);
      }
    }
  }

  module holes() {
    translate([z_rod_pos_x,0,0]) {
      hole(z_bearing_diam,z_printed_portion_height+1,resolution);

      translate([z_bearing_body_diam/2,0,extrusion_height]) {
        cube([z_bearing_body_diam,5,z_printed_portion_height],center=true);
      }
    }

    // arm mounting holes
    translate([(z_bed_support_pos_x-sheet_thickness/2-z_bed_support_mount_depth/2),0,0]) {
      for(z=[-2,-1,0,1,2]) {
        translate([-15,-z_bearing_body_diam/2-z_bed_support_mount_depth/2,z_support_arm_hole_spacing*z]) {
          rotate([0,90,0]) {
            hole(m3_nut_diam,30,6);
            hole(3,z_bearing_body_diam*3,8);
          }
        }
      }
    }

    // z axis main plate mounting holes
    translate([(z_bed_support_pos_x-sheet_thickness/2-z_bed_support_mount_depth-m3_nut_diam/2),15,0]) {
      for(z=[1:z_support_arm_hole_count]) {
        translate([0,-z_bearing_body_diam/2-z_bed_support_mount_depth/2,z_printed_portion_height/2-z_support_arm_hole_spacing*z]) {
          rotate([90,0,0]) {
            rotate([0,0,90]) {
              hole(m3_nut_diam,30,6);
              hole(3,z_bearing_body_diam*3,8);
            }
          }
        }
      }
    }
  }

  difference() {
    body();
    holes();
  }
}

module z_bed_plate() {
  support_arm_rod_dist_y = z_bearing_body_diam/2+z_build_platform_depth/2;
  fill_to_arm            = abs(abs(z_rod_pos_y-support_arm_rod_dist_y) - abs(build_pos_y));
  depth                  = z_build_platform_depth+fill_to_arm;
  rounded_diam           = bc_shoulder_width*2;
  rounded_diam           = 12;

  module body() {
    translate([0,fill_to_arm/2,0]) {
      hull() {
        for(x=[left,right]) {
          for(y=[front,rear]) {
            translate([(z_build_platform_width/2-rounded_diam/2)*x,(depth/2-rounded_diam/2)*y,0]) {
              accurate_circle(rounded_diam,resolution);
            }
          }
        }
      }
    }
  }

  module holes() {
    // z belt access
    hull() {
      for(x=[left,right]) {
        translate([(z_rod_pos_x-z_bearing_body_diam/2-rounded_diam-z_bed_support_mount_depth)*x,fill_to_arm+depth/2,0]) {
          accurate_circle(rounded_diam*2,resolution);
        }
      }
    }
    for(x=[left,right]) {
      translate([z_bed_support_pos_x*x,fill_to_arm,0]) {
        rotate([0,0,90]) {
          box_holes_for_side(z_build_platform_depth,4);
        }
      }
      for(y=[front,rear]) {
        translate([heatbed_hole_spacing_x/2*x,heatbed_hole_spacing_y/2*y,0]) {
          accurate_circle(heatbed_hole_diam,resolution);
        }
      }
    }

    // make it fit inside the top sheet for cutting
    /*
    for(side=[left,right]) {
      translate([z_build_platform_width/2*side,fill_to_arm+depth/2,0]) {
        rotate([0,0,45]) {
          square([24,24],center=true);
        }
      }
    }
    */
  }

  difference() {
    body();
    holes();
  }
}

module z_main_plate() {
  width                  = z_bed_support_pos_x*2-sheet_thickness;

  module body() {
    square([width,z_printed_portion_height],center=true);
  }

  module holes() {
    for(side=[left,right]) {
      translate([side*(width/2-z_bed_support_mount_depth-m3_nut_diam/2),0,0]) {
        for(z=[1:z_support_arm_hole_count]) {
          translate([0,z_printed_portion_height/2-z_support_arm_hole_spacing*z,0]) {
            accurate_circle(3,resolution);
          }
        }
      }
    }

    translate([0,z_printed_portion_height/2+z_carriage_bearing_offset_z]) {
      for(side=[top,bottom]) {
        translate([0,z_carriage_bearing_spacing/2*side]) {
          accurate_circle(3,resolution);
        }
      }
    }
  }

  difference() {
    body();
    holes();
  }
}

// laser cut support arm
module z_support_arm() {
  angle_length = build_y*.9;
  angle_height = z_printed_portion_height*.7;

  flat_bottom_len = sheet_thickness+z_bed_support_mount_depth;
  rounded_diam = 10;

  difference() {
    intersection() {
      box_side([z_build_platform_depth,z_printed_portion_height],[3,0,0,0]);
      hull() {
        translate([-z_build_platform_depth/2,z_printed_portion_height/2]) {
          square([flat_bottom_len*2,z_printed_portion_height*2],center=true);
        }
        translate([z_build_platform_depth/2,z_printed_portion_height/2]) {
          square([2,10],center=true);
        }
        translate([z_build_platform_depth/2-rounded_diam/2,z_printed_portion_height/2-flat_bottom_len+rounded_diam/2]) {
          accurate_circle(rounded_diam,resolution);
        }
      }
    }

    translate([-z_build_platform_depth/2+z_bed_support_mount_depth/2,0]) {
      for(z=[-2,-1,0,1,2]) {
        translate([0,z_support_arm_hole_spacing*z]) {
          accurate_circle(3,resolution);
        }
      }
    }
  }
}

module rod_clamp(diam,height=rod_clamp_height) {
  clamp_screw_x = diam/2 + 0.1 + m3_diam/2;
  body_diam     = diam + wall_thickness*2;
  rounded_diam  = m3_diam;

  module body() {
    hull() {
      hole(body_diam,height,resolution);

      for(side=[front,rear]) {
        translate([clamp_screw_x+m3_nut_diam/2,side*(body_diam/2-rounded_diam/2),0]) {
          hole(rounded_diam,height,16);
        }
      }
    }
  }

  module holes() {
    hole(diam,height+1,16);

    translate([clamp_screw_x,0,0]) {
      rotate([90,0,0]) {
        rotate([0,0,90]) {
          hole(m3_diam,body_diam+1,6);

          translate([0,0,body_diam/2]) {
            hole(m3_nut_diam,2,6);
          }
        }
      }
    }

    translate([body_diam/2,0,extrusion_height]) {
      cube([body_diam,diam*.6,height],center=true);
    }

    for(side=[top,bottom]) {
      translate([0,0,side*(height/2+extrusion_width/2)]) {
        bevel_hole(diam,extrusion_width,16);
      }
    }
  }

  difference() {
    body();
    holes();
  }
}

module z_brace_sheet() {
  belt_pos = front*(sheet_pos_y - sheet_thickness/2 - z_rod_pos_y);

  module body() {
    translate([0,-top_rear_brace_depth/2,0]) {
      box_side([z_brace_height,top_rear_brace_depth],[3,0,0,0]);
    }
  }

  module holes() {
    translate([z_brace_height/2-z_belt_anchor_height/2,0,0]) {
      for(side=[top,bottom]) {
        translate([z_belt_anchor_hole_spacing/2*side,belt_pos+tensioner_belt_dist_y,0]) {
          accurate_circle(nema17_screw_diam,resolution);
        }
      }
    }
  }

  difference() {
    body();
    holes();
  }
}

module z_axis() {
  module z_build_plate() {
    difference() {
      cube([heatbed_width,heatbed_depth,heatbed_thickness],center=true);

      for(x=[left,right]) {
        for(y=[front,rear]) {
          translate([heatbed_hole_spacing_x/2*x,heatbed_hole_spacing_y/2*y,0]) {
            hole(heatbed_hole_diam,heatbed_thickness+1,8);
          }
        }
      }
    }
  }

  translate([0,z_rod_pos_y,build_base_z-z_printed_portion_height/2]) {
    for(side=[left,right]) {
      mirror([1-side,0,0]) {
        printed_z_portion();
      }

      // z bearings
      for(end=[top,bottom]) {
        translate([z_rod_pos_x*side,0,end*(z_bearing_len/2 + z_bearing_spacing/2)]) {
          % hole(z_bearing_diam,z_bearing_len,16);
        }
      }

      // support arms
      translate([z_bed_support_pos_x*side,-z_bearing_body_diam/2-z_build_platform_depth/2-0.1,0]) {
        rotate([0,0,-90]) {
          rotate([90,0,0]) {
            color("purple") linear_extrude(height=sheet_thickness,center=true) {
              z_support_arm();
            }
          }
        }
      }
    }
  }

  translate([0,z_rod_pos_y-z_bearing_body_diam/2-z_bed_support_mount_depth-sheet_thickness/2,build_base_z-z_printed_portion_height/2]) {
    rotate([90,0,0]) {
      color("orange", sheet_opacity) linear_extrude(height=sheet_thickness,center=true) {
        z_main_plate();
      }
    }

    translate([0,sheet_thickness/2,z_printed_portion_height/2+z_carriage_bearing_offset_z]) {
      z_carriage_bearing_support_arm();
    }
  }

  translate([build_pos_x,build_pos_y,build_base_z+sheet_thickness/2]) {
    translate([0,0,sheet_thickness/2+1]) {
      color("red") {
        z_build_plate();
      }
    }

    linear_extrude(height=sheet_thickness,center=true) {
      z_bed_plate();
    }
  }
}

module tuner() {
  adjuster_narrow_neck_len = 2;
  adjuster_len = 24 - tuner_body_diam + adjuster_narrow_neck_len;
  adjuster_large_diam = 8;
  adjuster_tuner_thin_diam = 6;
  adjuster_x = tuner_body_pos;
  adjuster_y = tuner_body_square_len/2;
  adjuster_shaft_z = tuner_body_diam/2+adjuster_len/2;
  adjuster_paddle_len = 20;
  adjuster_paddle_z = adjuster_shaft_z + adjuster_len/2 + adjuster_paddle_len/2;
  adjuster_paddle_width = 17.8;
  adjuster_paddle_thickness = adjuster_tuner_thin_diam;

  module body() {
    //% translate([-tuner_hole_to_shoulder/2,-thick_diam,0]) rotate([0,90,0]) cylinder(r=tuner_thin_diam/4,h=tuner_hole_to_shoulder,center=true);

    // thin shaft
    translate([-tuner_thin_pos,0,0]) rotate([0,90,0])
      hole(tuner_thin_diam,tuner_thin_len,resolution);

    // thick shaft (area to clamp)
    translate([-thick_pos,0,0]) rotate([0,90,0])
      hole(thick_diam,thick_len,resolution);

    // body
    translate([tuner_body_pos,0,0]) {
      hull() {
        rotate([0,90,0]) {
          hole(tuner_body_diam,tuner_body_thickness,resolution);
        }
        translate([0,tuner_body_square_len/2,0]) {
          cube([tuner_body_thickness,tuner_body_square_len,tuner_body_diam],center=true);
        }
      }
    }

    // anchor screw hole
    translate([tuner_anchor_screw_hole_pos_x,0,0]) {
      hull() {
        translate([0,tuner_anchor_screw_hole_pos_y,tuner_anchor_screw_hole_pos_z]) rotate([0,90,0])
          hole(tuner_anchor_screw_hole_diam+tuner_anchor_screw_hole_width*2,tuner_anchor_screw_hole_thickness,resolution);
        rotate([0,90,0])
          hole(thick_diam,tuner_anchor_screw_hole_thickness);
      }
    }

    // twist adjuster
    translate([adjuster_x,adjuster_y,adjuster_shaft_z]) {
      hull() {
        translate([0,0,-adjuster_len/2-.5]) hole(adjuster_large_diam,1,resolution);
        translate([0,0,+adjuster_len/2-.5]) hole(adjuster_tuner_thin_diam,1,resolution);
      }
      // paddle, representing space taken when rotated
      hull() {
        //translate([0,0,adjuster_paddle_len/2]) cylinder(r=adjuster_paddle_width/2,h=1,center=true);
        //translate([0,0,1]) cylinder(r=adjuster_paddle_thickness/2,h=1,center=true);
        translate([0,0,adjuster_paddle_len-.5]) cube([adjuster_paddle_width,adjuster_paddle_thickness,1],center=true);
        translate([0,0,adjuster_len/2]) cube([adjuster_paddle_thickness,adjuster_paddle_thickness,1],center=true);
      }
    }
  }

  module holes() {
    cylinder(r=wire_hole_diam/3,h=tuner_thin_diam*2,center=true);

    translate([tuner_anchor_screw_hole_pos_x,tuner_anchor_screw_hole_pos_y,tuner_anchor_screw_hole_pos_z]) rotate([0,90,0])
      hole(tuner_anchor_screw_hole_diam,tuner_anchor_screw_hole_thickness+1,8);
  }

  difference() {
    body();
    holes();
  }
}

module position_z_pulley_bearing_retaimer_mount_holes() {
  diam              = bearing_625_diam + 0.1;
  offset            = 30;
  for(r=[0,120,240]) {
    rotate([0,0,offset+r]) {
      translate([diam/2+wall_thickness+m3_nut_diam/2,0,0]) {
        children();
      }
    }
  }
}

module z_idler_pulley_bearing_retainer() {
  diam              = bearing_625_diam + 0.1;
  bearing_body_diam = diam + wall_thickness*2;
  nut_hole_depth    = 2;

  module body() {
    hull() {
      hole(bearing_body_diam,z_idler_pulley_bearing_retainer_thickness, resolution);

      position_z_pulley_bearing_retaimer_mount_holes() {
        hole(m3_nut_diam+wall_thickness*3,z_idler_pulley_bearing_retainer_thickness,6);
      }
    }
  }

  module holes() {
    translate([0,0,z_idler_pulley_bearing_retainer_rim_thickness]) {
      hole(bearing_625_diam,z_idler_pulley_bearing_retainer_thickness,16);
    }
    hole(bearing_625_diam-2,z_idler_pulley_bearing_retainer_thickness*2,resolution);

    position_z_pulley_bearing_retaimer_mount_holes() {
      hole(3,z_idler_pulley_bearing_retainer_thickness+1,6);

      hull() {
        translate([0,0,-z_idler_pulley_bearing_retainer_thickness/2-0.05]) {
          hole(m3_nut_diam,(nut_hole_depth+0.05)*2,6);
          hole(m3_nut_diam+1,0.1,6);
        }
      }
    }
  }

  module bridges() {
    position_z_pulley_bearing_retaimer_mount_holes() {
      translate([0,0,-z_idler_pulley_bearing_retainer_thickness/2+nut_hole_depth+extrusion_height/2]) {
        hole(m3_nut_diam+0.05,extrusion_height,6);
      }
    }
  }

  difference() {
    body();
    holes();
  }
  bridges();
}

module bearing_625() {
  difference() {
    hole(bearing_625_diam,bearing_625_thickness,resolution);
    hole(bearing_625_inner,bearing_625_thickness+1,resolution);
  }
}

module filament_spool() {
  module body() {
    for(side=[left,right]) {
      translate([0,0,filament_spool_width/2*side]) {
        hole(filament_spool_outer_diam,4, resolution);
      }
      hole(filament_spool_core_diam,filament_spool_width, resolution);
    }
  }

  module holes() {
    hole(filament_spool_inner_diam,filament_spool_width*2,resolution);
  }

  difference() {
    body();
    holes();
  }
}
